TamojitSaha/Luminode/Sources/FirmWare/Pre-Alpha/NRF24L01P_chat_program/NRF24L01P_chat_program.ino

#include<SPI.h>
#include"nRf24L01.h"
#include"RF24.h"
#include"printf.h"
RF24 radio(9, 10);
const uint64_t pipes[2] = { 0xF0F0F0F0E1LL, 0xF0F0F0F0D2LL };
bool go_to_tx_mode = false;
char input[32] = "";
void setup()
{
  Serial.begin(57600);
  printf_begin();
  radio.begin();
  radio.setRetries(15, 15);
  radio.openWritingPipe(pipes[1]);
  radio.openReadingPipe(1, pipes[0]);
  radio.startListening();
  radio.printDetails();
}
void loop()
{
  if (go_to_tx_mode)
  {
    radio.stopListening();
    bool ok = radio.write(input, 32);
    if (ok)
    {
      printf("SENDER : %s\n", input);
      go_to_tx_mode = false;
      radio.startListening();
    }
    else
      printf("could not write....\n");
  }
  
  if (radio.available())
  {
    char payload[32] = "";
    bool done = false;
    while (!done)
    {
      done = radio.read( payload , 32 );
      printf("RECIEVER : %s\n", payload);
    }
  }
  
  if (Serial.available())
  { 
    int len = Serial.readBytesUntil('\n', input, 31);
    input[len] = '\0';
    go_to_tx_mode = true;
  }
}
/*
if (Serial.available())
{ 
  char txmsg[32];
  char buf[100]= Serial.read();
  int len= sizeof(buf);
  end=0;
  for(int i=0;end!=1;i=i+31)
  {
    if(i<len)&&(len<i+31)
    for(j=1;buf[i+j]!='\0';j++)
    {
      txm[j]=buf[i+j];
    }
    else
    for(j=1;j<31;j++)
    {
      txm[j]=buf[i+j];
    }
    if(j==30)
    {
      txm[31]='\0';
    }
    else
    end=1;
    go_to_tx(txm);
  }
}
*/
